dzooli/nodemcu-rgbstrip/include/rgbstrip_types.h

#ifndef __RGBSTRIP_TYPES_H__

#define __RGBSTRIP_TYPES_H__

struct rgbstatus
{
    unsigned char r;
    unsigned char g;
    unsigned char b;
    unsigned char l;
};

/* Program states and the current state */
/*
 * Not used yet
 *
enum {
  MODE_OFF,
  MODE_ON,
  MODE_FULL,
  MODE_SLEEP,
  MODE_FLASH,
  MODE_SMOOTH,
  MODE_LOVE
};
*/

#endif
